ivancornut/datalogger/Software/micropython/datalogger_class.py

from machine import Pin, PWM, Timer,I2C,lightsleep,WDT, idle, ADC,SPI, reset, deepsleep, disable_irq, enable_irq
from time import sleep
import sensor_class
import json
import sdcard
import vfs
import os
from ds3231 import DS3231
import urtc

class datalogger:
    """ A datalogger class to be used with any sensors
    that use a compatible sensor class """
    def __init__(self):
        
        ### Initial wait and led indication ###
        self.led = Pin(25, Pin.OUT) # internal led of the Pi Pico
        self.led.value(0)
        
        self.testing = False
        self.I2C_0_used = False # This is to know whether to initialise the I2C ports
        self.I2C_1_used = False # This is to know whether to initialise the I2C ports
        
        self.usb_pin = Pin(24, Pin.IN) # identifies if Pi Pico is plugged into a computer
        
        if self.usb_pin():
            self.blink_status("USB_conn")
            sleep(8) # time for the reset before setting the watchdog
        else:
            self.blink_status("start_ok")
            self.usb_pin.irq(handler = self.reset_datalogger, trigger=self.usb_pin.IRQ_RISING, hard=True)
            
        
         ### Watchdog ###
        """ The watchdog will reset the device if execution stops for whatever reason
        this is useful since bugs or unexpected errors can happen """
        self.watchdog = WDT(timeout=8000)
        
        try:
            with open('info.json','r') as f:
                config = json.load(f)
            self.file_prefix = config["device_name"]
            self.sensors = config["sensors"]
            self.timesteps = config["timesteps"]
            if "batt_R1" in config:
                batt_r1 = float(config["batt_R1"])
                batt_r2 = float(config["batt_R2"])
            else:
                batt_r1 = 22
                batt_r2 = 68
            
            if "rtc_type" in config: # to account for older versions of datalogger using the adafruit shield
                self.rtc_type = config["rtc_type"]
            else:
                self.rtc_type = "Adafruit"

        except Exception as e:
            print(e)
            with open('logs.txt','a') as f:
                f.write("Error reading info json:")
                f.write(str(e))
                f.write("\n")
            self.blink_status("no_info_file")
            self.blink_status(status="major_err")
            lightsleep(6500)
            reset()
            
        try:
            if self.rtc_type == "DS3232":
                self.I2C_0_obj = I2C(0,scl=Pin(5), sda=Pin(4))  # Correct I2C pins for RP2040
                self.I2C_0_used = True
                self.rtc = DS3231(self.I2C_0_obj) # for time
                sleep(0.2)
                self.rtc.output_32kHz(False)
            else:
                self.I2C_0_obj = I2C(0,scl=Pin(5), sda=Pin(4))
                self.rtc = urtc.PCF8523(self.I2C_0_obj)
                self.I2C_0_used = True     
        except Exception as e:
            print("Error in RTC setup:")
            print(e)
            self.blink_status(status="major_err") # Blink to indicate issue to user
            with open('logs.txt','a') as f:
                f.write("Error in RTC setup")
                f.write(str(e))
                f.write("\n")
            lightsleep(6500)
            reset()
        self.watchdog.feed()
        
        # create the sensor objects
        self.sensor_objs = []
        print(self.sensors)
        for s in self.sensors:
            try:
                obj = self.create_sensor(s)
                if obj is None:
                    print("Unknown or misconfigured sensor:", s)
                else:
                    self.sensor_objs.append(obj)
            except Exception as e:
                print("Error in creating sensor")
                print(e)
        
        self.watchdog.feed()
        self.battery_pin = ADC(26)
        self.voltage_drop_factor = 1/(batt_r1/(batt_r2+batt_r1))
        
        self.temp_sensor = ADC(4)
        self.battery_voltage = 12 # dummy to start in case below doesn't work
        self.read_battery_voltage()
        
        self.column_names = ["Battery_voltage","internal_temperature"] # initialise column names
        
        #!!!! New version that integrates SD card and precision RTC clock !!!!
        try:
            cs = Pin(17, Pin.OUT)
            spi= SPI(0, baudrate=1000000,polarity=0,phase=0,bits=8,firstbit=SPI.MSB,sck=Pin(18),mosi=Pin(19),miso=Pin(16))
            self.sd = sdcard.SDCard(spi, cs)
            self.filsys = vfs.VfsFat(self.sd)
        except Exception as e:
            print("Error in SD card setup:")
            print(e)
            self.blink_status(status="major_err") # Blink to indicate issue to user
            with open('logs.txt','a') as f:
                f.write("Error in SD card setup")
                f.write(str(e))
                f.write("\n")
            lightsleep(6000)
            reset()
        
        
        
        # the sensor objects will output the corresponding columns
        for sensor in self.sensor_objs:
            if sensor.exists:
                self.column_names = self.column_names + sensor.column_names
         
        # check if all timesteps are equal:
        val = self.timesteps[0]
        self.is_timer = False
        self.different_timesteps = len(set(self.timesteps)) > 1
        self.multi_files = self.different_timesteps
        if len(set(self.timesteps)) > 1:
            self.blink_status(status="major_err") # Blink to indicate issue to user
            print("Mixed timesteps not yet supported")
            lightsleep(6000)
            reset()
        
        self.watchdog.feed()
        if self.different_timesteps:
            # this is experimental does not work for now
            # Here we see if we need timers or rather to use the RTC for time intervall
            self.timers = []
            self.sensors_with_timers = []
            self.mini_timestep = 9999
            for i in timesteps:
                if i<60:
                    self.timers.append(Timer())
                    self.sensors_with_timers.append(sensor_nb)
                    self.is_timer=True
                else:
                    # mini timestep is the smallest timestep of the series
                    self.mini_timestep = min(i,self.mini_timestep) 
                sensor_nb = sensor_nb + 1
        else:
            if val<60:
                # this is experimental does not work for now
                self.interval = val
                self.unique_timer = Timer()
                self.is_timer = True
            else:
                self.interval = val
                self.watchdog.feed()
    
    def blink_status(self, status):
        if status=="start_ok":
            for i in range(0,3):
                sleep(1)
                self.led.toggle()
                sleep(0.3)
                self.led.value(0)
        elif status=="no_info_file":
            for i in range(0,15):
                sleep(0.3)
                self.led.toggle()
                sleep(0.3)
                self.led.value(0)
        elif status=="USB_conn":
            for i in range(0,6):
                sleep(1)
                self.led.toggle()
                sleep(0.3)
                self.led.value(0)
        elif status=="major_err":
            for i in range(0,5):
                self.led.toggle()
                sleep(0.2)
                self.led.toggle()
                sleep(0.2)
                self.led.toggle()
                sleep(0.2)
                self.led.toggle()
                sleep(0.8)
                self.led.value(0)
        else:
            return False
        
    def reset_datalogger(self, pin):
        reset()
    
    def read_battery_voltage(self):
        sensor_value = 0
        for i in range(0,10):
            sensor_value = sensor_value + self.battery_pin.read_u16()/10
        self.battery_voltage = sensor_value * (3.3 / 65535) * self.voltage_drop_factor
    
    def read_internal_temperature(self):
        adc_value = self.temp_sensor.read_u16()
        voltage = adc_value * (3.3 / 65535.0)
        self.internal_temp = 27 - (voltage - 0.706) / 0.001721
        
    def create_sensor(self,sensor):
        # This function initialises the different sensors
        sensor_name = sensor["type"]
        
        # !!! Campbell CS616 soil humidity probes !!!
        if sensor_name == "CS616": 
            p = sensor["params"]
            if self.rtc_type == "DS3232":
                if "corrected" in p:
                    if p["corrected"] == 1:
                        return sensor_class.TDR_CS616(nb_cs616=p["number"], meas_pin=p["measPin"],ctrl_pins = p["ctrlPins"], disable_pin = p["disabPin"],corrected = True,rtc = self.rtc)
            return sensor_class.TDR_CS616(nb_cs616=p["number"], meas_pin=p["measPin"],ctrl_pins = p["ctrlPins"], disable_pin = p["disabPin"])
        
        # !!! Fine Open dendros on ADS1115 !!!
        elif sensor_name == "dendro": 
            p = sensor["params"]
            if p["I2C"] == 0:
                if not self.I2C_0_used:
                    self.I2C_0_obj = I2C(0, sda=Pin(4), scl=Pin(5))
                    self.I2C_0_used = True
                return sensor_class.dendrometer(self.I2C_0_obj,on_pins=p["excite"],nb_dendros=p["number"],addr=p["address"], names=p["names"])
            elif p["I2C"] == 1: 
                if not self.I2C_1_used:
                    self.I2C_1_obj = I2C(1, sda=Pin(2), scl=Pin(3))
                    self.I2C_1_used = True
                return sensor_class.dendrometer(self.I2C_1_obj,on_pins=p["excite"],nb_dendros=p["number"],addr=p["address"], names=p["names"])
              
        # !!! SHT45 !!!
        elif sensor_name == "SHT45":
            p = sensor["params"]
            if p["I2C"] == 0:
                if not self.I2C_0_used:
                    self.I2C_0_obj = I2C(0, sda=Pin(4), scl=Pin(5))
                    self.I2C_0_used = True
                return sensor_class.temp_hum_sht45(self.I2C_0_obj, name = p["name"])
            elif p["I2C"] == 1:
                if not self.I2C_1_used:
                    self.I2C_1_obj = I2C(1, sda=Pin(2), scl=Pin(3))
                    self.I2C_1_used = True
                return  sensor_class.temp_hum_sht45(self.I2C_1_obj, name = p["name"])
        
        # !!! TMP1826 temperature sensor !!!
        elif sensor_name == "TMP1826":
            p = sensor["params"]
            return sensor_class.temp_tmp1826(meas_pin=p["meas_pin"])
            
    
    def _write_file(self,sensor_values,test = False):
        # read the diagnostics
        self.read_battery_voltage()
        self.read_internal_temperature()
        state = disable_irq()
        vfs.mount(self.filsys, "/sd") # mount the SD card7
        try:
            if self.multi_files:
                return None
            else:
                datetime = self.rtc.datetime() # check date
                if self.rtc_type == "DS3232":
                    year = datetime[0]
                    month = datetime[1]
                    day = datetime[2]
                    hour = datetime[4]
                    minute = datetime[5]
                    second = datetime[6]
                else:
                    year = datetime.year
                    month = datetime.month
                    day = datetime.day
                    hour = datetime.hour
                    minute = datetime.minute
                    second = datetime.second
                
                local_filename = self.file_prefix+'_'+str(year)+"-"+str(month)+"-"+str(day)+".csv"
                if test:
                    self.filename = "test.csv"
                    if not "test.csv" in os.listdir('/'):
                        # create the header of the file
                        with open(self.filename,'a') as f:
                            f.write("DateTime")
                            for i in self.column_names:
                                f.write(",")
                                f.write(i)
                            f.write("\n")    
                else:
                    self.filename = "/sd/"+local_filename
                    if not local_filename in os.listdir('/sd'):
                        # create the header of the file
                        with open(self.filename,'a') as f:
                            f.write("DateTime")
                            for i in self.column_names:
                                f.write(",")
                                f.write(i)
                            f.write("\n")    
                with open(self.filename,'a') as f:
                    # append the file with the newline of data
                    f.write(f"{year:04d}-{month:02d}-{day:02d}T{hour:02d}:{minute:02d}:{second:02d}")
                    f.write(",")
                    f.write(f"%1.2f" % self.battery_voltage)
                    f.write(",")
                    f.write(f"%1.1f" % self.internal_temp)
                    for sv in sensor_values:
                        for v in sv:
                            f.write(",")
                            f.write("%1.4f" % v)
                    f.write("\n")
        finally:
            vfs.umount("/sd") # unmount the SD card
            enable_irq(state)
        self.watchdog.feed()
    
    def _display_batt(self):
        if self.battery_voltage > 12.6:
            for i in range(0,3):
                sleep(0.1)
                self.led.value(1)
                sleep(0.02)
                self.led.value(0)
        elif self.battery_voltage <= 12.6 and self.battery_voltage > 12.4:
            for i in range(0,2):
                sleep(0.1)
                self.led.value(1)
                sleep(0.02)
                self.led.value(0)
        elif self.battery_voltage <= 12.4 and self.battery_voltage > 12.15:
            self.led.value(1)
            sleep(0.02)
            self.led.value(0)
        else:
            self.led.value(1)
            sleep(0.1)
            self.led.value(0)
        self.led.value(0)
    
    def _run_interval(self):
        """ This function is for sensors with measurement intervalls of
        more than a minute """
        self.interval_minutes = self.interval // 60
        while True:
            datetime = self.rtc.datetime() # check the datetime
            if self.rtc_type == "DS3232":
                hour = datetime[4]
                minute = datetime[5]
            else:
                hour = datetime.hour
                minute = datetime.minute

            if self.usb_pin():
                self.read_internal_temperature()
                # if connected to usb do not sleep
                # and instead read sensors every 4s
                print(self.sensor_objs)
                for sensor in self.sensor_objs:
                    if sensor.exists:
                        sensor.read_values(self.watchdog, self.led, debug = True)
                    self.watchdog.feed()
                print(f"Internal temp: %1.1f" % self.internal_temp)
                sleep(4)
            else:
                if (hour==0 and minute ==0):
                    # this is to reset the datalogger once a day.
                    if (minute%self.interval_minutes) == 0: # check whether it is time to log
                        values = []
                        for sensor in self.sensor_objs:
                            if sensor.exists:
                                values.append(sensor.read_values(self.watchdog,self.led))
                            self.watchdog.feed()
                        self._write_file(values)
                        for i in range(0,10):
                            self.watchdog.feed()
                            lightsleep(6000)
                    reset()
                if (minute%self.interval_minutes) == 0: # check whether it is time to log
                    values = []
                    for sensor in self.sensor_objs:
                        if sensor.exists:
                            values.append(sensor.read_values(self.watchdog,self.led))
                        self.watchdog.feed()
                    self._write_file(values)
                    
                    # Then sleep to keep energy
                    for i in range(0,6*self.interval_minutes):
                        lightsleep(6500)
                        self.watchdog.feed()
                        self._display_batt()
                else:
                    for i in range(0,4):
                        lightsleep(6500)
                        self.watchdog.feed()
                        self._display_batt()
                    
    def _run_test(self):
        while True:
            values = []
            for sensor in self.sensor_objs:
                if sensor.exists:
                    values.append(sensor.read_values(self.watchdog,self.led))
                else:
                    print("Error sensor doesn't exist")
                    print(sensor)
                self.watchdog.feed()
            self._write_file(values, test = True)
            sleep(5)
            
    def _run_timers(self):
        return None
     
    def run(self):
        if self.testing:
            self._run_test()
        else:
            if self.is_timer:
                self._run_timers()
            else:
                self._run_interval()
        
